alexKrsn1234/Cimino-Krausener-PEIP2-ARDUINO-PROJECT-/code/telecommunication/HC-12/AT commands/transmitter/emmeteur1.ino

#include <SoftwareSerial.h>

SoftwareSerial HC12(10,11); // HC-12 TX Pin, HC-12 RX Pin

void setup() {
  Serial.begin(9600);             // Serial port to computer
  HC12.begin(9600);               // Serial port to HC12

}

void loop() {
  while (HC12.available()) {        // If HC-12 has data
    Serial.write(HC12.read());      // Send the data to Serial monitor
  }
  while (Serial.available()) {      // If Serial monitor has data
    HC12.write(Serial.read());      // Send that data to HC-12
  }
}
